TechMaverik/ROB/static/StudioDevice.png

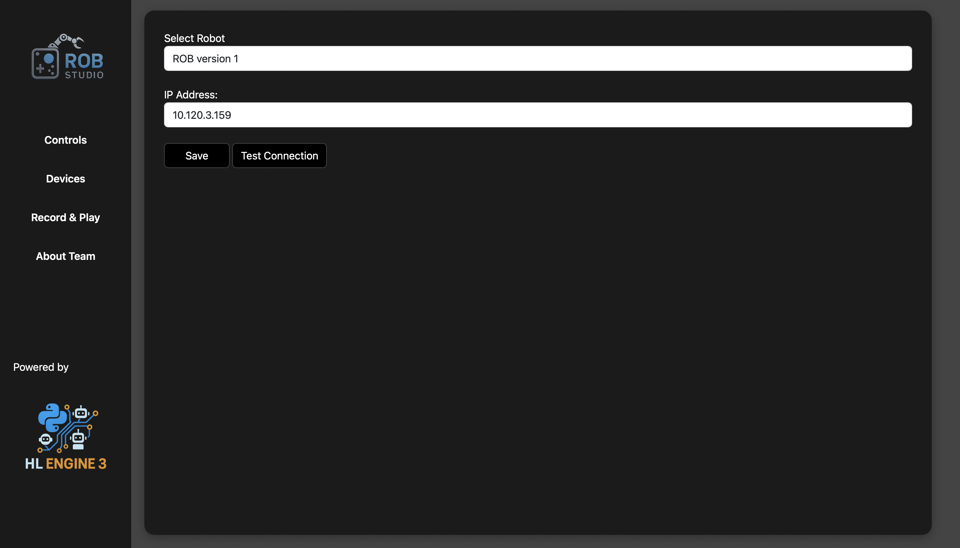
static/StudioDevice.png
