TechMaverik/ROB/Firmware/prepositions.py

HOME_POS = {
    "base": 90,  # 0-180
    "shoulder": 90,  # 15-165
    "elbow": 90,  # 0-180
    "wrist": 90,  # 0-180
    "end_effector": 90,  # 10-73
    "pick": 90,
}

TEST_POS_MAX = {
    "base": 179,  # 0-180
    "shoulder": 165,  # 15-165
    "elbow": 179,  # 0-180
    "wrist": 179,  # 0-180
    "end_effector": 73,  # 10-73
    "pick": 180,
}

TEST_POS_MIN = {
    "base": 0,  # 0-180
    "shoulder": 15,  # 15-165
    "elbow": 0,  # 0-180
    "wrist": 0,  # 0-180
    "end_effector": 10,  # 10-73
    "pick": 0,
}

TEST_BASE_MIN = {
    "base": 60,  # 0-180
    "shoulder": 60,  # 15-165
    "elbow": 60,  # 0-180
    "wrist": 60,  # 0-180
    "end_effector": 60,  # 10-73
    "pick": 80,
}

TEST_BASE_MAX = {
    "base": 130,  # 0-180
    "shoulder": 130,  # 15-165
    "elbow": 130,  # 0-180
    "wrist": 130,  # 0-180
    "end_effector": 130,  # 10-73
    "pick": 150,
}
